domoticawifi/Network-nodes/img/Foto/IMG_20170404_150251.jpg

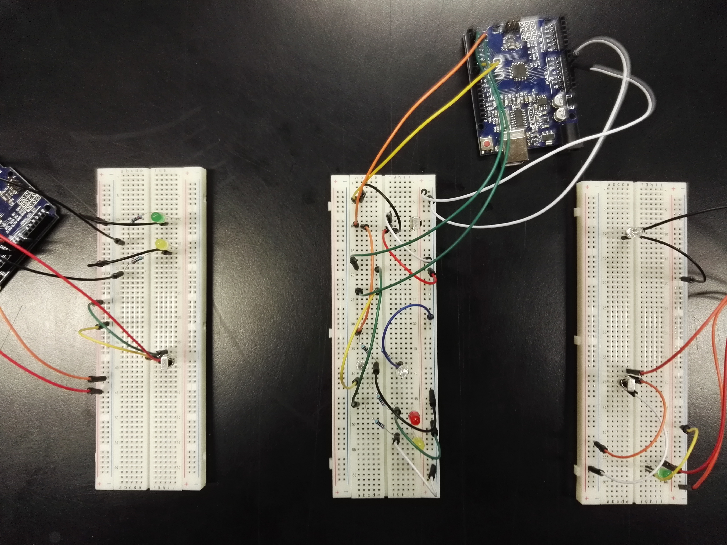
img/Foto/IMG_20170404_150251.jpg
