domoticawifi/Network-nodes/img/Loghi/net.png

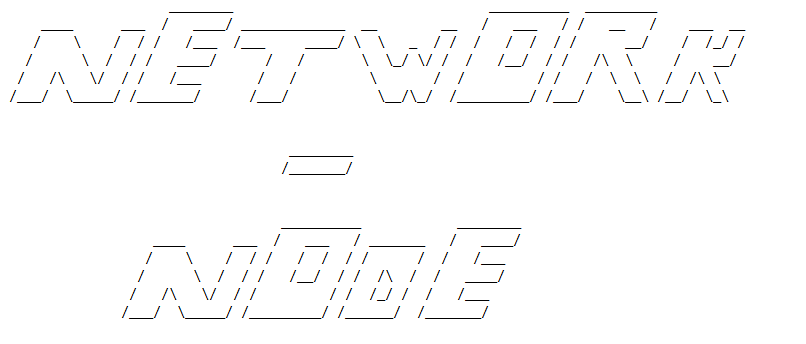
img/Loghi/net.png
